citizensense/AirKit_Logbook/images/3.25_rev2_bold_in_bottom.jpeg

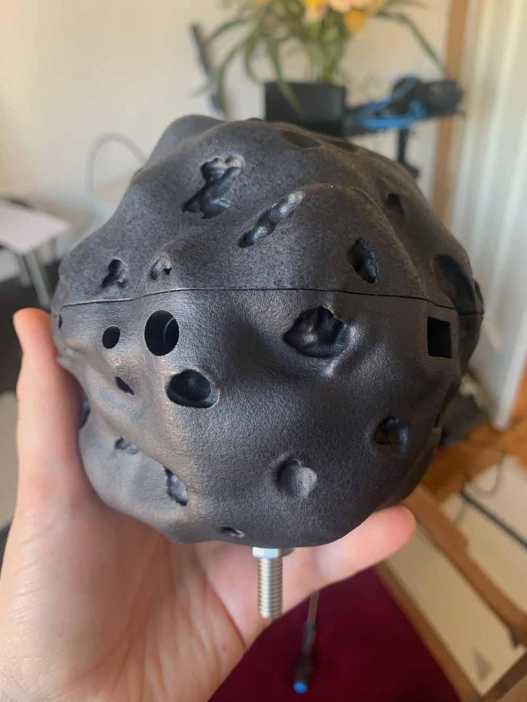
images/3.25_rev2_bold_in_bottom.jpeg
