citizensense/AirKit_Logbook/images/4.13_holding_phone_data_piping_nice_hand.JPG

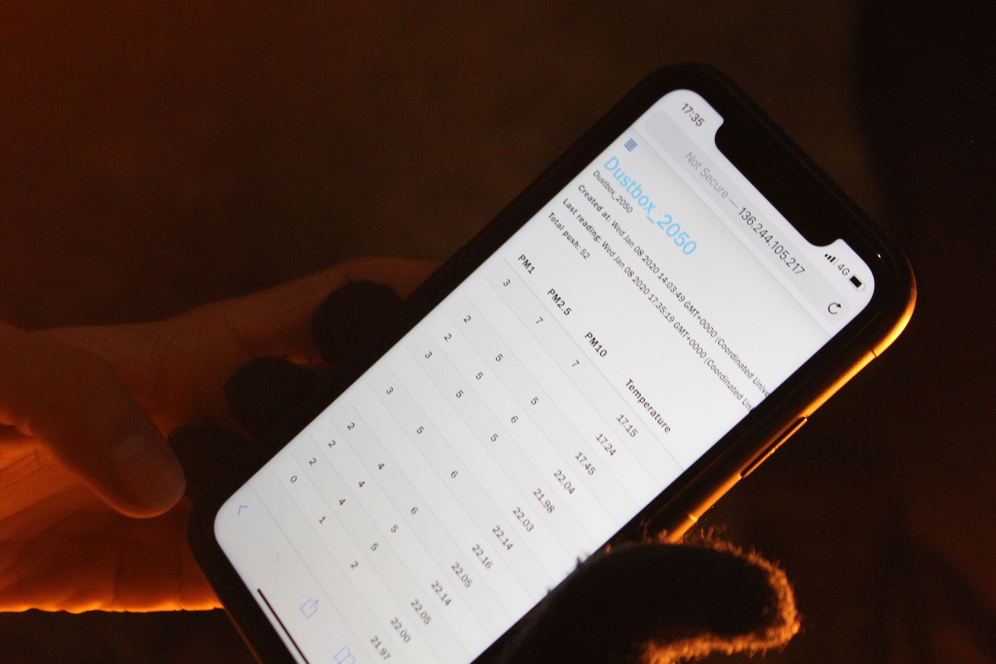
images/4.13_holding_phone_data_piping_nice_hand.JPG
