citizensense/AirKit_Logbook/images/README_dustbox_fully_assembled_close_up_more_devices_in_focus.JPG

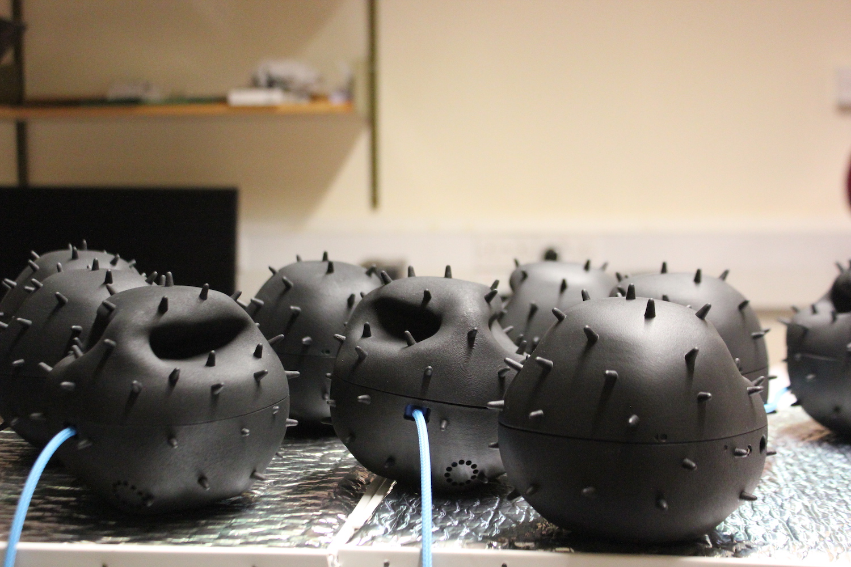
images/README_dustbox_fully_assembled_close_up_more_devices_in_focus.JPG
